mohoyt/lagom/img/diode pin closeup.jpg

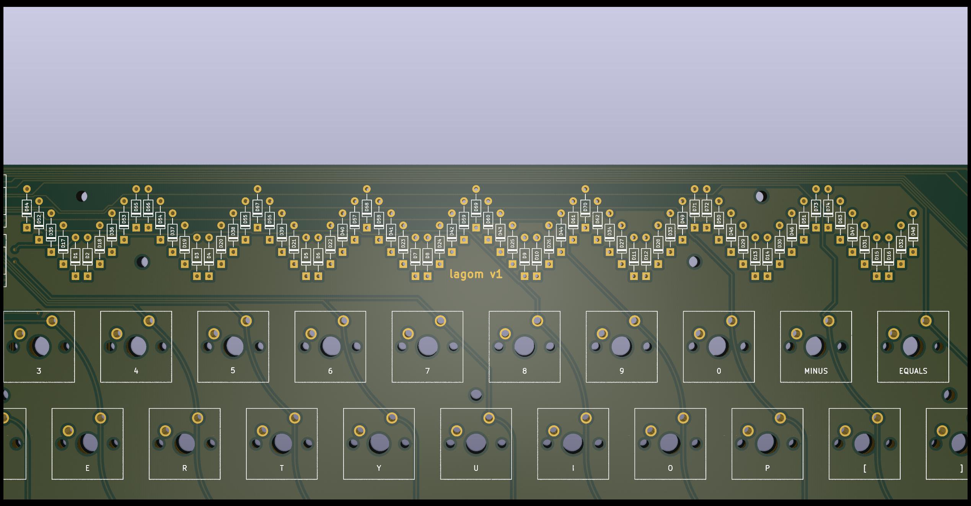
img/diode pin closeup.jpg
